karaulj/onechuk/components/device_profile/include/RedDeviceProfile.h

/*
 * RedDeviceProfile.h
 *
 *  R device profile - System info, nunchuk sensor readouts, restart
 * 
 *  Created on: Jun 14, 2021
 *      Author: Jacob
 */

#ifndef COMPONENTS_MAIN_PROFILES_RED_DEVICE_PROFILE_H_
#define COMPONENTS_MAIN_PROFILES_RED_DEVICE_PROFILE_H_

#include "IDeviceProfile.h"


class RedDeviceProfile: public IDeviceProfile
{
public:
    void profileSelectedCallback();
    void gestureClickCallback();
    void gestureUpCallback();
    void gestureDownCallback();
    void gestureLeftCallback();
    void gestureRightCallback();
    void gestureCircleCallback();
};


#endif /* COMPONENTS_MAIN_PROFILES_RED_DEVICE_PROFILE_H_ */
